sensemakersamsterdam/openThermostat/case/openThermostat-Case-Prototype1-Closed.jpg

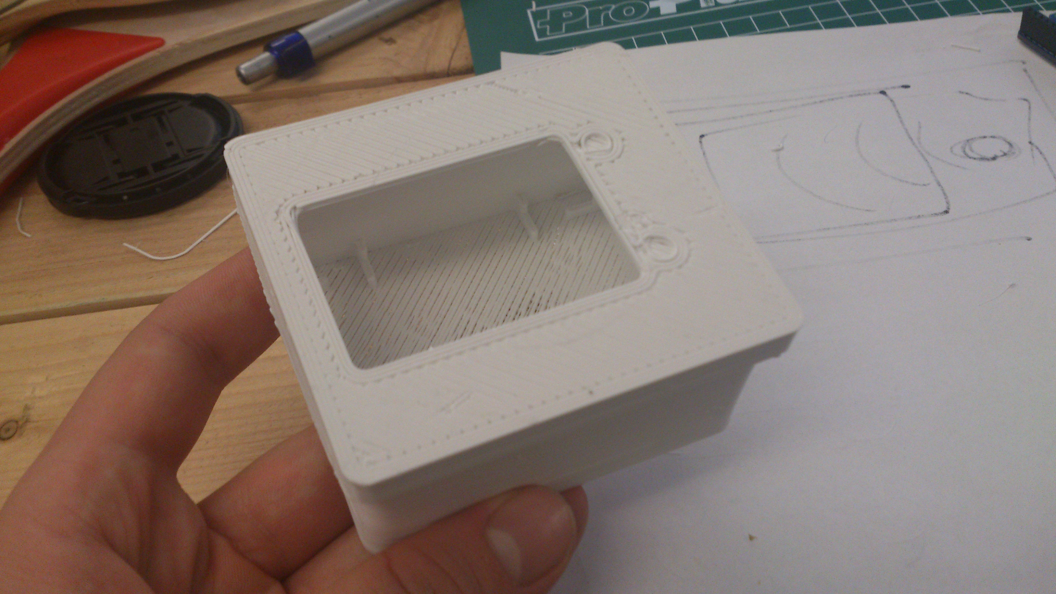
case/openThermostat-Case-Prototype1-Closed.jpg
