sensemakersamsterdam/openThermostat/case/openThermostat-Case-Prototype1-Open.jpg

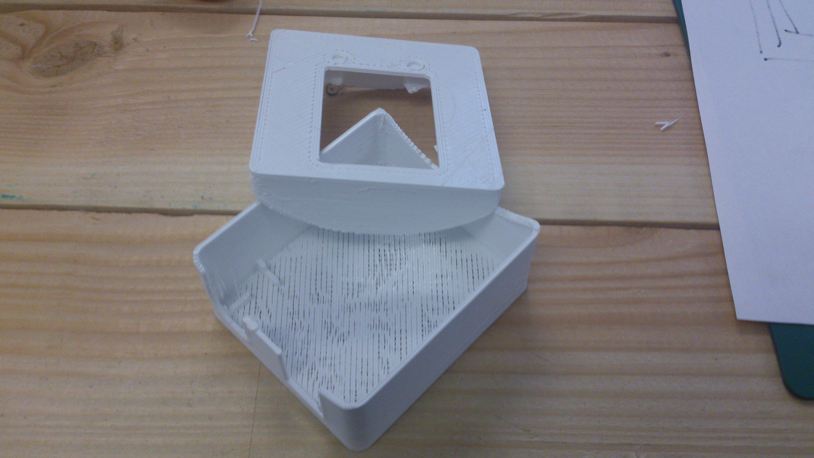
case/openThermostat-Case-Prototype1-Open.jpg
