sensemakersamsterdam/openThermostat/doc/scenario1.jpg

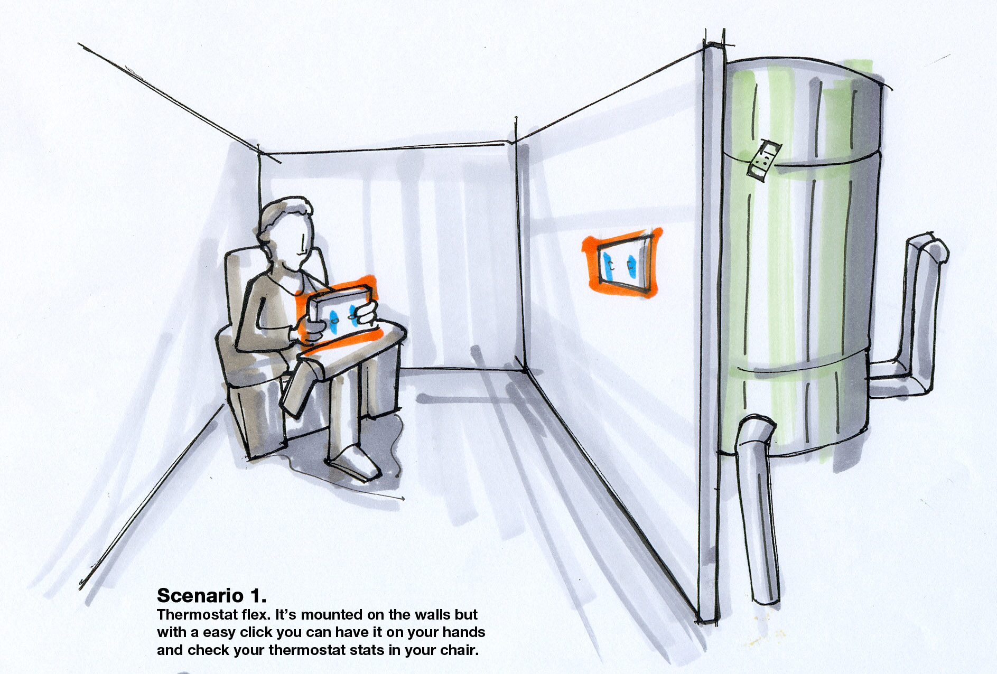
doc/scenario1.jpg
