sensemakersamsterdam/openThermostat/doc/scenario2.jpg

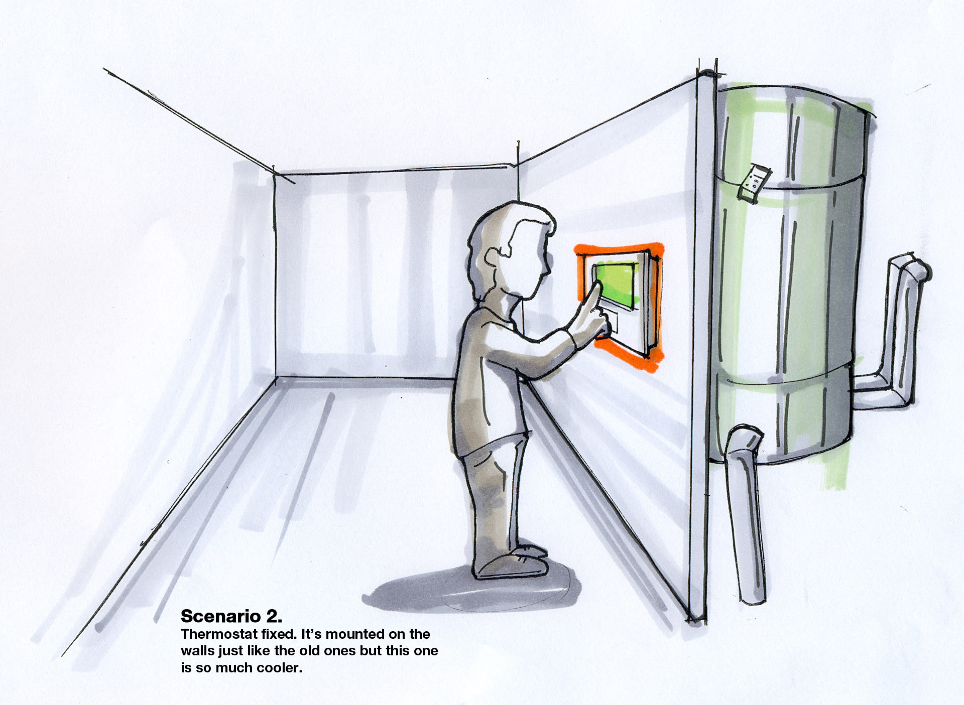
doc/scenario2.jpg
