sensemakersamsterdam/openThermostat/doc/scenario3.jpg

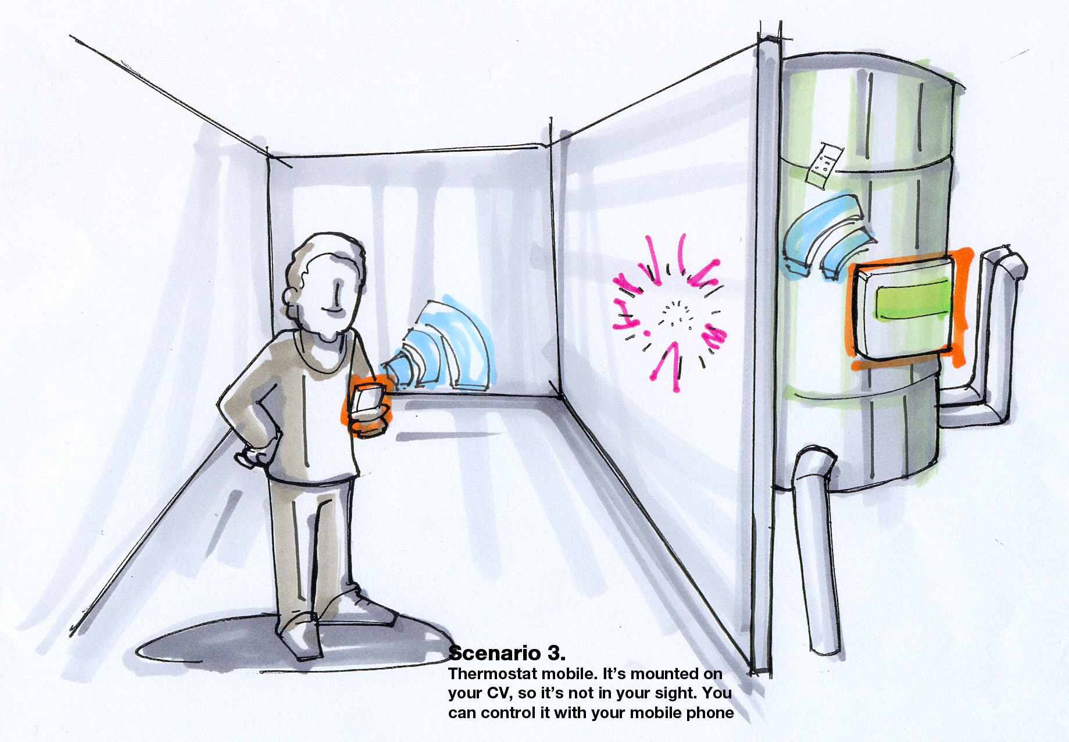
doc/scenario3.jpg
