sensemakersamsterdam/openThermostat/doc/sensornode.jpg

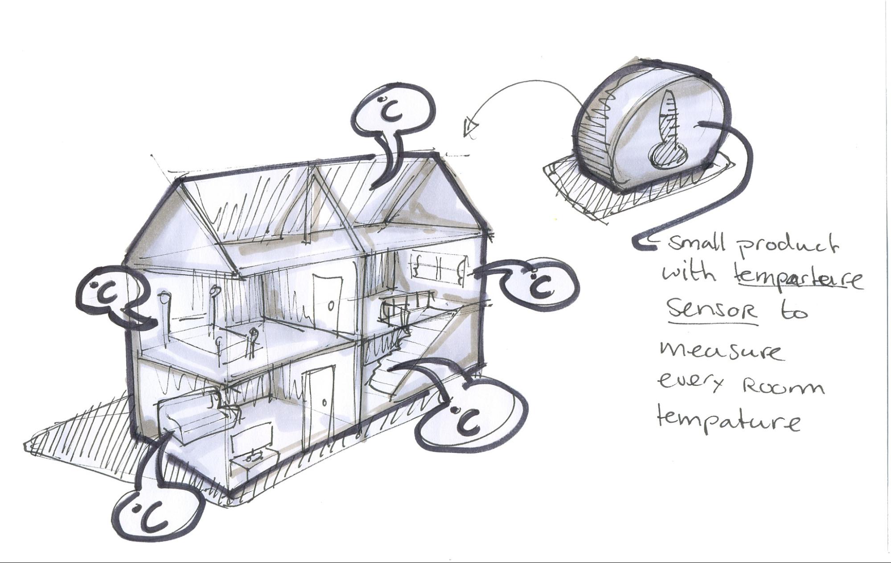
doc/sensornode.jpg
