sensemakersamsterdam/openThermostat/doc/smartphone-integration.jpg

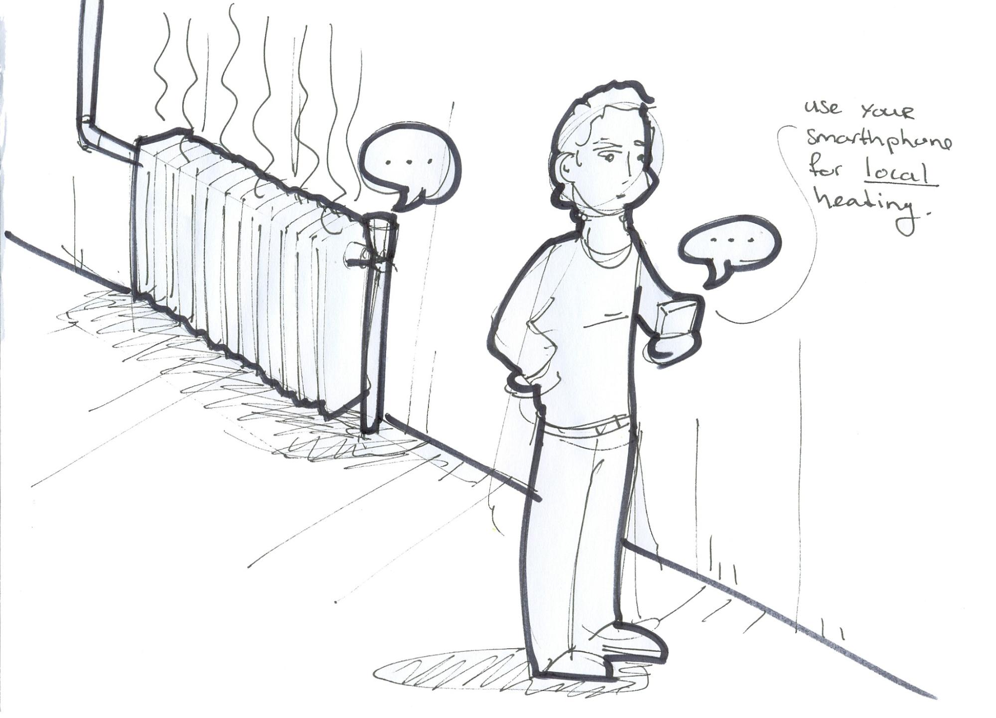
doc/smartphone-integration.jpg
