sensemakersamsterdam/openThermostat/PCB/pictures/openThermostatShield-PCB1.png

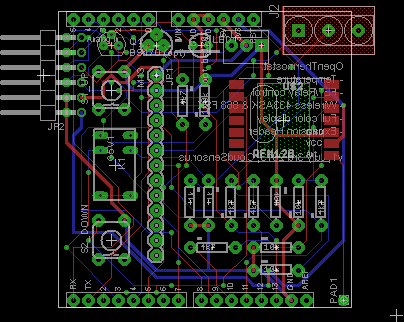
PCB/pictures/openThermostatShield-PCB1.png
