sensemakersamsterdam/openThermostat/PCB/pictures/openThermostatShield-PCB2.png

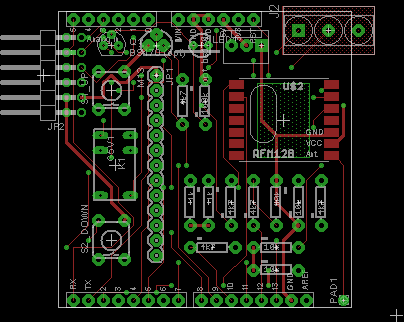
PCB/pictures/openThermostatShield-PCB2.png
