sensemakersamsterdam/openThermostat/PCB/pictures/openThermostatShield-PCB4.png

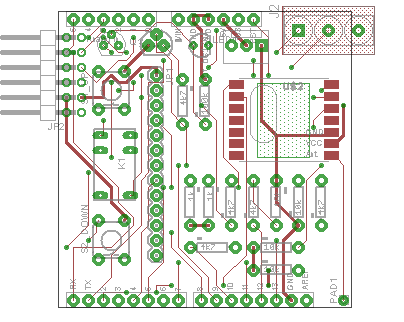
PCB/pictures/openThermostatShield-PCB4.png
