sensemakersamsterdam/openThermostat/photos/openThermostatShield-Bottom.jpg

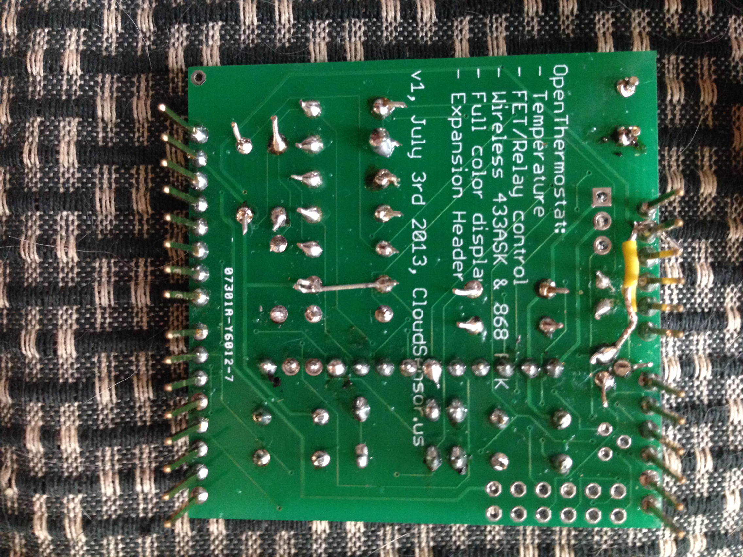
photos/openThermostatShield-Bottom.jpg
