sensemakersamsterdam/openThermostat/photos/openThermostatShield-on-Arduino1.jpg

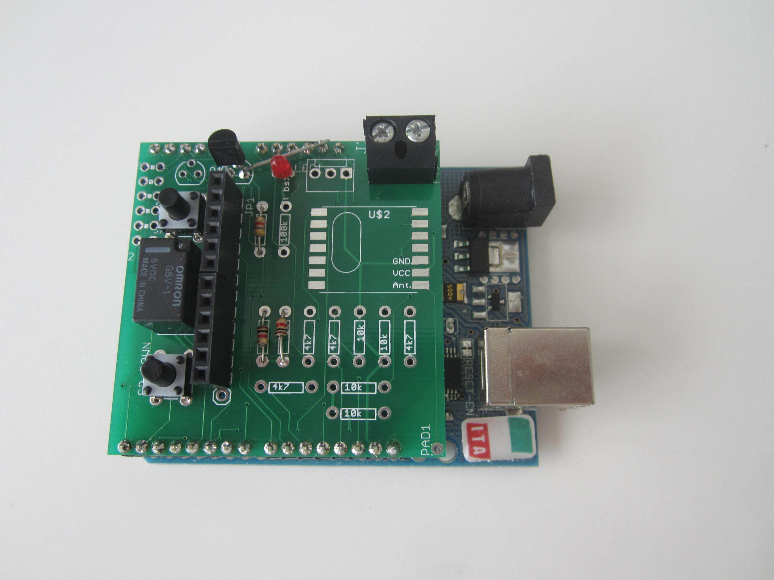
photos/openThermostatShield-on-Arduino1.jpg
