sensemakersamsterdam/openThermostat/photos/openThermostatShield-on-Arduino2.jpg

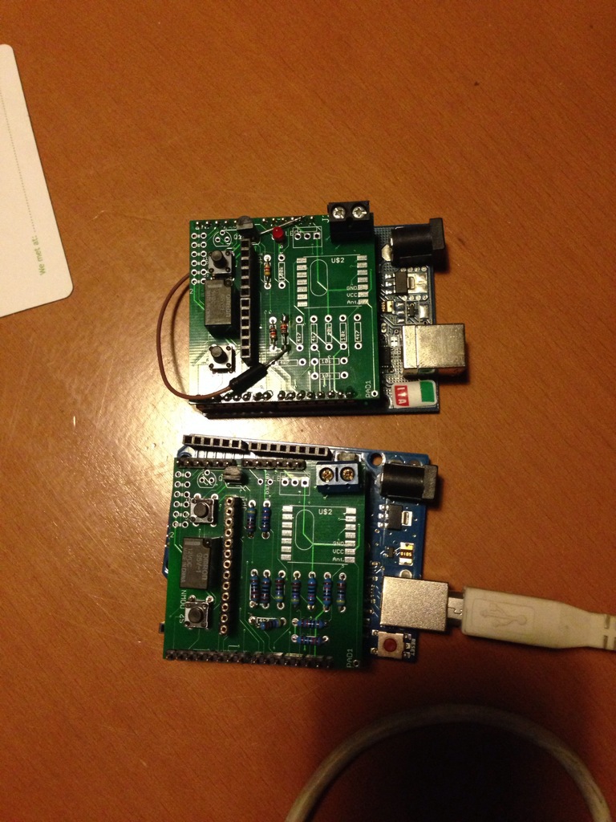
photos/openThermostatShield-on-Arduino2.jpg
