sensemakersamsterdam/openThermostat/photos/openThermostatShield-Top.jpg

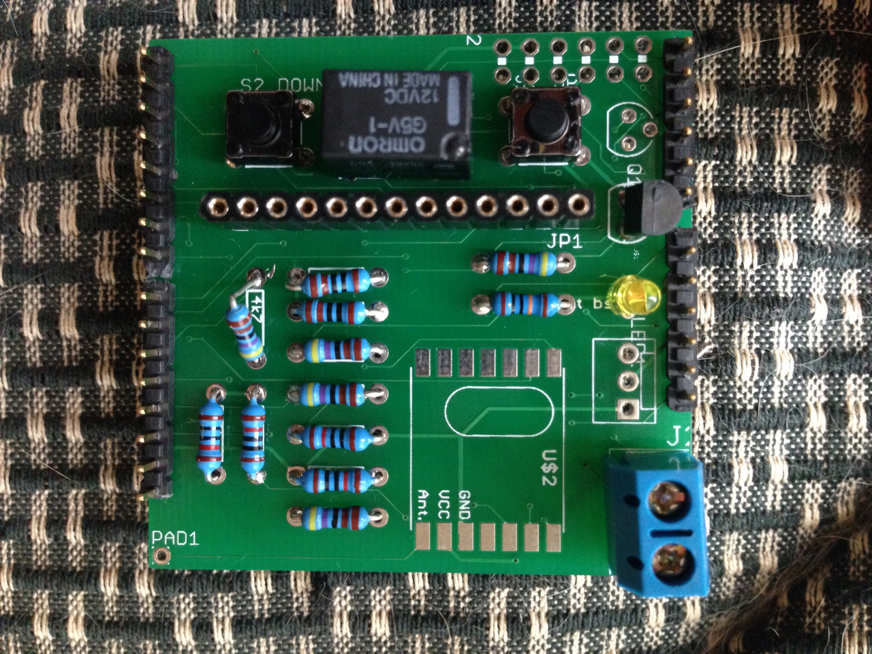
photos/openThermostatShield-Top.jpg
